P47Phoenix/Claude-Keyboard/claude-code-pad/case/PARAMS.md

# Claude Code Pad — Case parameters

All parameters live at the top of `claude-code-pad.py`. Tweak and re-run
to regenerate the STL / STEP outputs. Dimensions in millimetres.

## Shrinkage compensation (Cycle 2)

| Parameter | Default | Purpose |
| --- | --- | --- |
| `SHRINK_COMPENSATION` | 0.005 | Factor by which every INNER cutout is upscaled so the cooled part lands on nominal. 0.5 % is a K2-Plus / PETG baseline — **calibrate per-printer / per-filament**. |
| `COUPON_SHRINK_STEPS` | `[0.003, 0.005, 0.007]` | Three row-wise shrink values baked into `test-coupon.stl` so a single print reveals which value clips MX switches cleanly. |

The compensation is applied via `_shrink(nominal)` to: MX cutouts, 2U
stab slots + wire holes, the encoder knob hole, M3 clearance holes in
the plate, the USB-C slot, the slide-switch window, and the heat-set
insert pilot holes. It is **not** applied to outer shells or wall
thicknesses (outer walls shrink inward — scaling the shell up would
make the case oversized). See `README.md` §Print calibration for the
coupon-driven calibration procedure.

## Board constants (read from PCB Edge.Cuts, aux origin = 100, 100)

| Parameter | Default | Purpose |
| --- | --- | --- |
| `BOARD_W` | 120.0 | PCB east-west extent. |
| `BOARD_H` | 132.0 | PCB north-south extent. |
| `BOARD_THICKNESS`  | 1.6 | FR4 thickness. Drives placeholder height and assembly Z. |
| `BOARD_CORNER_R` | 3.0 | PCB corner fillet radius. |
| `USBC_NOTCH_X` | 54.0 | West edge of the USB-C notch in the north PCB edge (local X). |
| `USBC_NOTCH_W` | 12.0 | Width of the USB-C notch. |

## Key grid (5 × 5, MX hotswap + 2U Enter at row 4 col 4)

| Parameter | Default | Purpose |
| --- | --- | --- |
| `KEY_PITCH` | 19.05 | Standard 1U MX pitch. |
| `KEY_CUTOUT` | 14.0 | MX switch plate cutout nominal (before shrinkage). |
| `COL_X` | `[19.4, 38.45, 57.5, 76.55, 95.6]` | Column centres (board-local X). |
| `ROW_Y` | `[39.525, 58.575, 77.625, 96.675, 115.725]` | Row centres. |
| `ENTER_KEY_CENTRE` | `(105.125, 115.725)` | 2U Enter centre (col 4 + 0.5U east offset). |
| `STAB_OFFSET` | 11.9 | Cherry 2U stab slot offset (c-to-c, E or W of key). |
| `STAB_SLOT_W` | 3.97 | Stab slot width (E-W). |
| `STAB_SLOT_H` | 6.65 | Stab slot height (N-S). |
| `STAB_WIRE_HOLE_D` | 3.05 | Wire relief hole diameter. |
| `STAB_WIRE_OFFSET_N` | 2.3 | Wire hole offset N of key centre. |

## Peripheral feature positions (board-local coords)

| Parameter | Default | Purpose |
| --- | --- | --- |
| `ENCODER_CENTRE` | `(108.0, 19.0)` | EC11 rotary-encoder centre (PCB footprint). |
| `ENCODER_KNOB_D` | 16.0 | Knob access hole Ø in top plate (Cycle 2: 10 → 16 for a 14 mm knob + 1 mm clearance). |
| `ENCODER_KNOB_PROTRUSION`  | 6.0 | Height the encoder knob extends above the top-plate top face. |
| `ENCODER_PRESS_TRAVEL` | 1.0 | EC11 tactile press-click axial travel clearance. |
| `XIAO_CENTRE` | `(60.0, 19.0)` | U1 centre (XIAO module). |
| `SWITCH_CENTRE` | `(33.0, 19.0)` | SPDT slide switch (SW_PWR1) centre. |
| `JST_CENTRE` | `(8.0, 19.0)` | J_BAT1 JST-PH centre (cable exits -X). |
| `NTC_CENTRE` | `(10.0, 24.0)` | TH1 NTC thermistor centre (thermal membrane, not through-hole — Cycle 2). |
| `SWITCH_WINDOW_W` | 12.0 | Cycle 2: 8 → 12 (MSS22AG15 slider body 11 mm + 1 mm clearance). |
| `SWITCH_WINDOW_H` | 6.0 | Cycle 2: 4 → 6 (actuator boss 5 mm + 1 mm clearance). |
| `USBC_SLOT_W` | 15.0 | Cycle 2: 14 → 15 to clear host-cable boot (plug body 8.3, boot typical 11, target +3 pad).  |
| `USBC_SLOT_H` | 10.0 | Same (plug + boot). |
| `USBC_BRIDGE_W` | 1.0 | Sacrificial mid-span bridge width (print-time aid, removed post-print). |
| `USBC_BRIDGE_H` | 2.0 | Sacrificial mid-span bridge height (centred in slot). |
| `USBC_EDGE_CHAMFER` | 1.0 | 1 × 1 mm 45° external-edge chamfer on USB-C aperture for plug-boot lead-in. |

## Mounting holes (board-local)

| Parameter | Default |
| --- | --- |
| `MOUNT_HOLES` | `[(3.5, 27), (116.5, 27), (5.0, 128), (115.0, 128)]` — matches PCB H1..H4. |

## Antenna keepout (XIAO nRF52840)

| Parameter | Default | Purpose |
| --- | --- | --- |
| `ANTENNA_KEEPOUT_CENTRE` | `(60.0, 19.0)`  | Keepout patch centre (board-local). |
| `ANTENNA_KEEPOUT_W` | 25.0 | Keepout E-W extent. |
| `ANTENNA_KEEPOUT_H` | 10.3 | Keepout N-S extent. |
| `ANTENNA_KEEPOUT_CLEARANCE`  | 5.0 | No metal / heat-set inserts within this ring around the keepout rect. |

Bosses whose centres fall inside `keepout + clearance` are printed with a
2.8 mm pilot hole for direct self-tap into PETG (no metal insert).

With the current PCB, the keepout envelope (incl. 5 mm clearance) spans
case-frame X = 42.5..77.5, Y = 8.85..29.15. The 4 mounting bosses sit at
case (5.90, 29.40), (118.90, 29.40), (7.40, 130.40), (117.40, 130.40) —
**all four are outside the envelope in X**, so all four use heat-set
inserts. No boss demotion is needed at this PCB revision. If ECE-1 moves
H1 or H2 inward in a future revision, `build_bottom_case()` will
auto-demote them to self-tap.

## Battery bay (Adafruit #1578 — 500 mAh LiPo, 50 × 34 × 7 mm)

| Parameter | Default | Purpose |
| --- | --- | --- |
| `BATT_BAY_W` | 54.0 | Cell + 2 mm clearance per side (E-W). |
| `BATT_BAY_H` | 38.0 | Same, N-S. |
| `BATT_BAY_DEPTH` | 9.0 | Cell + 2 mm vertical clearance. |
| `BATT_BAY_CENTRE` | `(30.0, 75.0)` | Bay centre in board-local frame (inboard of JST side).  |

## Safety features

| Parameter | Default | Purpose |
| --- | --- | --- |
| `VENT_HOLE_D` | 3.0 | Cycle-2 vent geometry: round holes (Ø 3) in place of Cycle-1 slots (bridging failure mode on PETG). |
| `FLOOR_VENT_OFFSETS` | 12 × `(dx, dy)` | 4×3 grid of Ø 3 holes in the bay floor (~85 mm²). Cycle 3: 8 → 12 to lift total vent area over the 150 mm² target. |
| `WALL_VENT_Z` | `[D-6.5, D-4.25, D-2.0]` | Three Z heights for wall vents (relative to floor, D = `BATT_BAY_DEPTH`). Cycle 3: 2 → 3 levels. |
| `WALL_VENT_Y_OFFSETS`  | `[-8.0, 8.0]` | Y offsets for wall-vent pairs, giving 6 holes per east/west wall (12 wall vents total across both walls). |
| `DIVIDER_SLOT_T` | 1.8 | Groove width for the 1.6 mm FR-4 divider (slide fit). |
| `DIVIDER_HEIGHT` | = `BATT_BAY_DEPTH` | Divider spans full bay depth. |
| Divider retention | 3-edge (N + E + W) | Cycle-2 MAJOR #12: grooves on all three walls, not just north. |
| `JST_EXIT_W` | 2.5 | Width of the JST-PH cable pinch-slot in the divider. |
| `JST_EXIT_H` | 4.0 | Height of same. |
| Battery-bay wall thickness | 2.0 mm | Cycle-2 MAJOR #6: 1.5 → 2.0 for stiffness + UL flame-retention margin. |

**Total vent area (Cycle 3 corrected):** floor 12 × π (1.5)² ≈ 85 mm² +
walls 6 × π (1.5)² ≈ 42 mm² per side × 2 sides = 85 mm² →
≈ 170 mm² through floor + walls combined (well above the 150 mm²
MECH-1 target). With the FR-4 divider in place, the through-divider
path adds more egress if the divider includes builder-drilled weep
holes.

Cycle 2 numerics were incorrect (claimed 168 mm², actual = 113 mm² at
that geometry -- 16 × 7.07 mm² ≈ 113). Cycle 3 increased vent count
from 16 → 24 to reach the documented area.

**Strain relief (Cycle 2 MAJOR #11): cable gate.** The Cycle 1 Ø 2 mm
cantilever post is gone. In its place: a pair of 2 mm-thick PETG walls
standing 6 mm tall inside the bay, 2 mm apart, directly behind the
cable exit. The JST-PH cable passes BETWEEN the walls so any pull-out
force is resisted as wall-on-wall SHEAR (much stiffer than a 2 mm
cantilever). No wrap-around required.

## Wall / plate / mating geometry

| Parameter | Default | Purpose |
| --- | --- | --- |
| `PLATE_THICKNESS` | 1.8 | MX clip spec is 1.5 +/- 0.3; 1.8 mm plate sits at the **top of spec** (Cycle 3 dropped from 2.0 -> 1.8 to stay in-spec; 2.0 mm was outside the Cherry MX datasheet). Keypress stiffness retains ~88 % of the 2.0-mm box-section value once lip + walls are factored in. Test-click one MX switch before printing a full top case. |
| `TOP_WALL_THICKNESS` | 2.0 | Top-case sidewall / lip thickness. |
| `TOP_LIP_DEPTH` | 2.5 | How far the top lip drops into the bottom case for alignment. |
| `TOP_LIP_CLEARANCE` | 0.4 | Slip-fit gap between top lip outside and bottom wall inside (Cycle 2: bumped from 0.3 per real-PETG fit data). |
| `LIP_CHAMFER` | 0.5 | 45 deg lead-in chamfer on the top-lip bottom outer edge, **and** matching relief chamfer on the bottom-case interior wall top edge. |
| `BOTTOM_WALL_THICKNESS` | 2.0 | Bottom-case sidewall thickness. |
| `BOTTOM_FLOOR_THICKNESS` | 2.0 | Bottom-case floor thickness. |
| `PCB_TRAY_STANDOFF` | 5.0 | Cycle 2 MINOR #18: 3 → 5 to clear Kailh MX hot-swap socket tails (≈ 3.2 mm below PCB). Total case height rises correspondingly. |
| `PLATE_TO_PCB_GAP` | 5.0 | MX switch lower housing extends 5 mm below plate. |
| `BOTTOM_INTERIOR_HEIGHT` | derived | `max(standoff + pcb + plate_gap, batt_bay_depth + 1)` — whichever is taller. |
| `BOTTOM_WALL_TOP_Z` | derived | Mating-plane Z (top of bottom wall = bottom of top plate). |

## Heat-set insert bosses

| Parameter | Default | Purpose |
| --- | --- | --- |
| `INSERT_DIA` | 4.0 | Pilot Ø for M3 brass heat-set insert (CNC Kitchen IUB-M3-L4 nominal, pre-shrinkage). Shrink-compensated at cut time. |
| `INSERT_DEPTH`  | 4.2 | Pilot depth = IUB-M3-L4 length (4.0 mm) + 0.2 mm float so the insert never hard-stops on the pilot floor. |
| `BOSS_OD` | 8.0 | Boss outer Ø (**2.0 mm** wall around insert, Cycle-2 uprating of the 1.45 mm Cycle-1 wall — PETG fractures at 1.45 mm with knurl-induced hoop stress). |
| `BOSS_HEIGHT` | 6.7 | `INSERT_DEPTH + 2.5` — 2.5 mm solid PETG floor under the insert. |

Matching screw: **M3 × 6 mm** (plate 1.8 + lip 2.5 landed = **4.3 mm**
of clamped material ahead of the insert, so the screw engages
**1.7 mm** into the IUB-M3-L4 insert; M3 × 8 over-inserts and
bottoms in the insert's blind end). Cycle 3 updated the stack
math after PLATE_THICKNESS moved 2.0 -> 1.8 mm to sit within the
MX plate spec.

## Case outer geometry + feet

| Parameter | Default | Purpose |
| --- | --- | --- |
| `CASE_FIT_CLEARANCE` | 0.4 | PCB-to-wall clearance per side. |
| `CASE_OUTER_W` | derived | `BOARD_W + 2*(BOTTOM_WALL + CASE_FIT_CLEARANCE)` ≈ 124.8 mm. |
| `CASE_OUTER_H` | derived | Same idiom for height ≈ 136.8 mm. |
| `CASE_OUTER_R` | 6.0 | Outer corner fillet (Cycle 2 MINOR #17: 4 → 6 for cool-down stress distribution and better hand-feel). |
| `FOOT_D` | 12.7 | Rubber-foot recess Ø. Default matches **3M SJ-5018** (12.7 × 1 mm). For the Cycle-1 **3M SJ-5003** (10 × 1 mm), set to 10.0 and `FOOT_INSET` to 8.0. |
| `FOOT_DEPTH` | 1.0 | Recess depth (both 5003 and 5018 are 1 mm tall). |
| `FOOT_INSET` | 9.0 | Recess centre inset from case corner (matched to `FOOT_D = 12.7`). |

## Tuning tips

- **MX switch too tight:** bump `KEY_CUTOUT` from 14.0 → 14.10.
- **Top lip won't seat:** bump `TOP_LIP_CLEARANCE` from 0.3 → 0.5.
- **Screw won't bite insert:** re-flow the insert (see `README.md` §
  post-processing) before changing `INSERT_DIA`.
- **Battery won't fit:** `BATT_BAY_W/H/DEPTH` are already +2 mm per axis;
  only bump if switching to a larger cell.
- **Antenna failing RF range:** confirm `ANTENNA_KEEPOUT_CENTRE` matches
  your PCB's XIAO position and `ANTENNA_KEEPOUT_CLEARANCE` ≥ 5.0 mm.
