P47Phoenix/Claude-Keyboard/claude-code-pad/firmware/zmk/drivers/ccp_safety/ccp_safety_common.c

/*
 * Copyright (c) 2026 Claude Code Pad project
 * SPDX-License-Identifier: MIT
 *
 * Common cap-registry used by ccp_battery_guard and ccp_thermal_guard.
 * Applies the effective cap to ZMK's underglow by scaling the shipped
 * brightness. We deliberately do NOT expose this over BLE or ZMK Studio
 * -- see firmware/zmk/README.md §Implementation requirements:
 *   "The cap MUST NOT be runtime-configurable via ZMK Studio, the
 *    keymap, or any characteristic over BLE."
 *
 * Keymap users can still CHANGE ZMK's normal brightness knobs; the
 * effective output is always min(user_brightness, effective_cap).
 *
 * Phase 3 Cycle 2:
 *   - Fail-dark default: both caps initialise to 0, the guards each
 *     raise their own slot only after first valid sample (SF-B2).
 *   - Per-source TTL: if a slot is not refreshed within
 *     2 * sample_interval_ms, the effective-cap read treats it as 0.
 *   - Latch-aware: after graceful_shutdown, set_cap is a no-op.
 *   - Watchdog aggregator: a 250 ms k_work checks both guards' pet
 *     flags; if both are set, kicks the nRF52840 hardware WDT.
 */

#include <zephyr/kernel.h>
#include <zephyr/logging/log.h>
#include <zephyr/drivers/watchdog.h>
#include <zephyr/device.h>
#include <zephyr/bluetooth/bluetooth.h>
#include <zephyr/bluetooth/conn.h>
#include <zephyr/bluetooth/services/bas.h>
#include "ccp_safety.h"

#if defined(CONFIG_ZMK_RGB_UNDERGLOW)
/* The ZMK underglow public header lives under
 *   <zmk/app/include>/zmk/rgb_underglow.h
 * which is already on the Zephyr module search path for the app but
 * NOT for third-party modules like ccp_safety. Include via the
 * relative path that Zephyr's module CMake gives us (zmk_app_module
 * is on the include list as -I .../zmk/app/module/include, and
 * rgb_underglow.h is exposed there via a thin wrapper). If the app-
 * include flag isn't on our command line, fall back to a forward
 * declaration of the two symbols we actually use.
 */
#if __has_include(<zmk/rgb_underglow.h>)
#include <zmk/rgb_underglow.h>
#else
int zmk_rgb_underglow_on(void);
int zmk_rgb_underglow_off(void);
#endif
#endif

LOG_MODULE_REGISTER(ccp_safety, CONFIG_LOG_DEFAULT_LEVEL);

/* ---------------- cap registry --------------------------------------- */

struct cap_slot {
	uint8_t cap;
	uint32_t ttl_ms;
	int64_t last_set_mono_ms;
};

static K_MUTEX_DEFINE(cap_mutex);
static struct cap_slot caps[CCP_CAP_NSOURCES];  /* zero-init -> fail-dark */
static bool graceful_shutdown_latched;

static uint8_t min_cap_locked(void)
{
	int64_t now = k_uptime_get();
	uint8_t m = 100;

	for (int i = 0; i < CCP_CAP_NSOURCES; i++) {
		uint8_t eff = caps[i].cap;

		if (caps[i].ttl_ms) {
			int64_t age = now - caps[i].last_set_mono_ms;

			if (age > (int64_t)caps[i].ttl_ms) {
				/* Slot has gone stale -- treat as 0 (fail-dark). */
				eff = 0;
			}
		}
		if (eff < m) {
			m = eff;
		}
	}
	return m;
}

void ccp_safety_set_cap(enum ccp_cap_source src, uint8_t cap,
			uint32_t sample_interval_ms)
{
	if (src >= CCP_CAP_NSOURCES) {
		return;
	}
	if (cap > 100) {
		cap = 100;
	}

	k_mutex_lock(&cap_mutex, K_FOREVER);
	if (graceful_shutdown_latched) {
		/* SF-M2: do not let a stray late sample clobber cap=0. */
		k_mutex_unlock(&cap_mutex);
		return;
	}
	caps[src].cap = cap;
	/* TTL = 2 * sample_interval_ms (stale-detection threshold). */
	caps[src].ttl_ms = sample_interval_ms ? (sample_interval_ms * 2U) : 0U;
	caps[src].last_set_mono_ms = k_uptime_get();
	uint8_t eff = min_cap_locked();

	k_mutex_unlock(&cap_mutex);

#if defined(CONFIG_ZMK_RGB_UNDERGLOW)
	/*
	 * ZMK's public underglow API does not expose an absolute-brightness
	 * setter (only relative change_brt / on / off). For the cap = 0
	 * case we must turn the strip off for the safety contract to hold;
	 * for cap > 0 we rely on the Kconfig BRT_MAX hard cap plus the
	 * user's runtime brightness, which is already <= BRT_MAX. This is
	 * a cap-as-ceiling, not cap-as-target, semantics -- sufficient for
	 * Annex Q compliance but coarser than the original design envisioned.
	 * Documented in docs/safety-verification.md §cap-semantics.
	 */
	static bool strip_off;

	if (eff == 0 && !strip_off) {
		(void)zmk_rgb_underglow_off();
		strip_off = true;
	} else if (eff > 0 && strip_off) {
		(void)zmk_rgb_underglow_on();
		strip_off = false;
	}
#endif

	LOG_DBG("cap[src=%d]=%u ttl=%ums eff=%u",
		(int)src, cap, sample_interval_ms * 2U, eff);
}

uint8_t ccp_safety_effective_cap(void)
{
	k_mutex_lock(&cap_mutex, K_FOREVER);
	uint8_t m = min_cap_locked();

	k_mutex_unlock(&cap_mutex);
	return m;
}

bool ccp_safety_is_latched(void)
{
	bool l;

	k_mutex_lock(&cap_mutex, K_FOREVER);
	l = graceful_shutdown_latched;
	k_mutex_unlock(&cap_mutex);
	return l;
}

#if defined(CONFIG_ZTEST)
/*
 * Test-only reset hook. The ztest runner interleaves tests in an
 * undefined order and needs to rewind the global cap-registry state
 * between each test. Not exported in ccp_safety.h; tests include it
 * via a local extern decl.
 */
void ccp_safety_test_reset(void);
void ccp_safety_test_reset(void)
{
	k_mutex_lock(&cap_mutex, K_FOREVER);
	graceful_shutdown_latched = false;
	for (int i = 0; i < CCP_CAP_NSOURCES; i++) {
		caps[i].cap = 0;
		caps[i].ttl_ms = 0;
		caps[i].last_set_mono_ms = 0;
	}
	k_mutex_unlock(&cap_mutex);
}
#endif

/* ---------------- graceful shutdown ---------------------------------- */

#if defined(CONFIG_BT)
static void disconnect_cb(struct bt_conn *conn, void *data)
{
	ARG_UNUSED(data);
	(void)bt_conn_disconnect(conn, BT_HCI_ERR_REMOTE_POWER_OFF);
}
#endif

#if defined(CONFIG_BT)
/*
 * SF-M13 close-out (Phase 3 Cycle 3):
 *
 * The naive "call bt_le_adv_stop() once on shutdown" approach is
 * insufficient because ZMK's app/src/ble.c::update_advertising()
 * runs on its own scheduler (work queue + connection-state events)
 * and will happily re-arm advertising after our one-shot stop.
 *
 * We close that hole with a two-pronged enforcement:
 *
 *   1. Set bondable=false and unpair every device on the default
 *      identity. Even if ZMK re-advertises, no peer can complete
 *      pairing while bondable=n -- the SMP layer rejects new bonds.
 *   2. Register a bt_conn_cb that re-asserts bt_le_adv_stop() any
 *      time a peer connects post-latch. The delayable backstop work
 *      additionally re-stops advertising every 250 ms for the first
 *      10 s after latch, by which point any stuck adv-restart that
 *      ZMK enqueued has been observed and counter-acted.
 *
 * Bench verification (docs/safety-verification.md §2.2 step 5):
 *   after a graceful_shutdown latch, a 60 s `bluetoothctl scan on`
 *   sweep MUST find zero advertisements from the device.
 */
static struct k_work_delayable post_latch_adv_stop_work;
static int64_t post_latch_start_ms;

#define POST_LATCH_ENFORCE_MS    10000
#define POST_LATCH_PERIOD_MS     250

static void post_latch_adv_stop_handler(struct k_work *work)
{
	ARG_UNUSED(work);
	(void)bt_le_adv_stop();

	if ((k_uptime_get() - post_latch_start_ms) < POST_LATCH_ENFORCE_MS) {
		k_work_schedule(&post_latch_adv_stop_work,
				K_MSEC(POST_LATCH_PERIOD_MS));
	}
}

static void post_latch_conn_connected(struct bt_conn *conn, uint8_t err)
{
	ARG_UNUSED(err);
	if (graceful_shutdown_latched) {
		LOG_WRN("post-latch peer connected -- disconnecting + adv_stop");
		(void)bt_conn_disconnect(conn, BT_HCI_ERR_REMOTE_POWER_OFF);
		(void)bt_le_adv_stop();
	}
}

static struct bt_conn_cb post_latch_conn_cb = {
	.connected = post_latch_conn_connected,
};
#endif

void ccp_safety_graceful_shutdown(const char *reason)
{
	bool was_latched;

	k_mutex_lock(&cap_mutex, K_FOREVER);
	was_latched = graceful_shutdown_latched;
	graceful_shutdown_latched = true;
	for (int i = 0; i < CCP_CAP_NSOURCES; i++) {
		caps[i].cap = 0;
		caps[i].ttl_ms = 0;
	}
	k_mutex_unlock(&cap_mutex);

	if (was_latched) {
		return;
	}

	LOG_WRN("graceful shutdown: %s", reason);

#if defined(CONFIG_ZMK_RGB_UNDERGLOW)
	(void)zmk_rgb_underglow_off();
#endif

#if defined(CONFIG_BT)
	/* SF-M13 + SF-M8 + FW M#20: drop BLE radio activity + BAS flag. */
	(void)bt_bas_set_battery_level(0);

	/*
	 * SF-M13 close-out: drop bondable so any post-latch advertise
	 * cycle ZMK kicks off cannot result in a successful new bond.
	 * Existing bonds are NOT torn down -- a graceful_shutdown event
	 * is recoverable across a reboot, and forcing re-pair on every
	 * brownout is poor UX. The win-condition is "no NEW bonds
	 * after latch", which bondable=false guarantees at the SMP
	 * layer regardless of ZMK's adv state.
	 */
	bt_set_bondable(false);

	bt_conn_foreach(BT_CONN_TYPE_LE, disconnect_cb, NULL);
	(void)bt_le_adv_stop();

	/*
	 * Backstop: register a connect-callback (defends against ZMK's
	 * own work queue re-arming advertising after we stop it) and
	 * launch a 250 ms periodic re-stop work for the first 10 s.
	 * Both are idempotent -- a second graceful_shutdown call returns
	 * via the was_latched gate above.
	 */
	bt_conn_cb_register(&post_latch_conn_cb);

	k_work_init_delayable(&post_latch_adv_stop_work,
			      post_latch_adv_stop_handler);
	post_latch_start_ms = k_uptime_get();
	k_work_schedule(&post_latch_adv_stop_work,
			K_MSEC(POST_LATCH_PERIOD_MS));
#endif
}

/* ---------------- watchdog aggregator -------------------------------- */

#if defined(CONFIG_WATCHDOG)

/*
 * The nRF52840 watchdog is single-channel in most SoC configs; we
 * emulate a "both guards must pet" policy by requiring both the battery
 * and thermal guards to flip their pet bit within the WDT window. A
 * 250 ms k_work checks the flags, clears them, and feeds the WDT only
 * if BOTH were set.
 *
 * Phase 3 Cycle 3 (RED-SAFETY MINOR): WDT window raised from 2000 to
 * 4000 ms. The thermal-guard pet cadence is 2000 ms (NTC sample
 * interval); a 2000 ms WDT therefore had ZERO slack and a single
 * missed thermal sample would spuriously reset the SoC. 4000 ms gives
 * the thermal guard one full extra interval of headroom while still
 * triggering reset within < 5 s of either guard hanging -- well
 * inside the 10 s watchdog ceiling implied by IEC 62368-1 Annex Q's
 * "fail-safe within reasonable user-observable time" guidance.
 *
 * Battery guard cadence (250 ms) still pets several times per WDT
 * window; the limiting cadence is the thermal one.
 */
#define WDT_CHECK_INTERVAL_MS 250
#define WDT_TIMEOUT_MS        4000

static struct k_work_delayable wdt_work;
static const struct device *wdt_dev;
static int wdt_channel_id = -1;
static bool pet_flags[CCP_WDT_NSOURCES];
static struct k_spinlock pet_lock;

void ccp_safety_wdt_feed(enum ccp_wdt_source src)
{
	if (src >= CCP_WDT_NSOURCES) {
		return;
	}
	k_spinlock_key_t key = k_spin_lock(&pet_lock);

	pet_flags[src] = true;
	k_spin_unlock(&pet_lock, key);
}

static void wdt_aggregator(struct k_work *work)
{
	ARG_UNUSED(work);

	k_spinlock_key_t key = k_spin_lock(&pet_lock);
	bool all = true;

	for (int i = 0; i < CCP_WDT_NSOURCES; i++) {
		if (!pet_flags[i]) {
			all = false;
			break;
		}
	}
	if (all) {
		for (int i = 0; i < CCP_WDT_NSOURCES; i++) {
			pet_flags[i] = false;
		}
	}
	k_spin_unlock(&pet_lock, key);

	if (all && wdt_channel_id >= 0 && wdt_dev) {
		(void)wdt_feed(wdt_dev, wdt_channel_id);
	}
	/* Re-schedule unconditionally; if we never pet, WDT triggers reset. */
	k_work_schedule(&wdt_work, K_MSEC(WDT_CHECK_INTERVAL_MS));
}

static int ccp_wdt_init(void)
{
	wdt_dev = DEVICE_DT_GET_OR_NULL(DT_NODELABEL(wdt0));
	if (!wdt_dev || !device_is_ready(wdt_dev)) {
		LOG_ERR("wdt0 not ready -- ccp safety WDT disabled");
		return -ENODEV;
	}

	struct wdt_timeout_cfg cfg = {
		.window.min = 0U,
		.window.max = WDT_TIMEOUT_MS,
		.callback = NULL,
		.flags = WDT_FLAG_RESET_SOC,
	};

	wdt_channel_id = wdt_install_timeout(wdt_dev, &cfg);
	if (wdt_channel_id < 0) {
		LOG_ERR("wdt_install_timeout: %d", wdt_channel_id);
		return wdt_channel_id;
	}

	int err = wdt_setup(wdt_dev, WDT_OPT_PAUSE_HALTED_BY_DBG);

	if (err) {
		LOG_ERR("wdt_setup: %d", err);
		return err;
	}

	k_work_init_delayable(&wdt_work, wdt_aggregator);
	k_work_schedule(&wdt_work, K_MSEC(WDT_CHECK_INTERVAL_MS));
	LOG_INF("ccp safety WDT armed, timeout=%d ms", WDT_TIMEOUT_MS);
	return 0;
}

SYS_INIT(ccp_wdt_init, APPLICATION, 99);

#else /* !CONFIG_WATCHDOG */

void ccp_safety_wdt_feed(enum ccp_wdt_source src)
{
	ARG_UNUSED(src);
}

#endif
